SparksAndCode/Lock-Picking-Robot-V2/robot/Lock_Pick_v2 v76 v20_Lock_Pick_v2 v76 v20_5972K173_Ball Bearing_1_Body1.stl

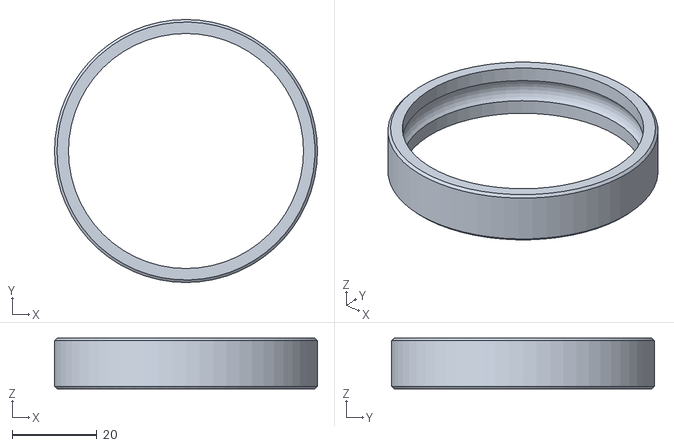
[picture p11: CAD file, 2024-05-01]
robot/Lock_Pick_v2 v76 v20_Lock_Pick_v2 v76 v20_5972K173_Ball Bearing_1_Body1.stl
62.0 x 62.0 x 12.0
