SparksAndCode/Lock-Picking-Robot-V2/robot/Lock_Pick_v2 v76 v20_Lock_Pick_v2 v76 v20_Lock Clamp_1_LockClamp_top.stl

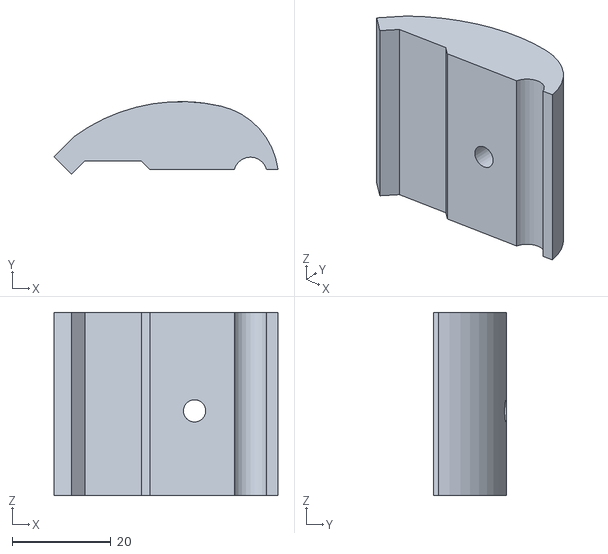
[picture p12: CAD file, 2024-05-01]
robot/Lock_Pick_v2 v76 v20_Lock_Pick_v2 v76 v20_Lock Clamp_1_LockClamp_top.stl
45.3 x 14.7 x 37.0
