SparksAndCode/Lock-Picking-Robot-V2/robot/Lock_Pick_v2 v76 v20_Lock_Pick_v2 v76 v20_Lock Clamp_1_LockClamp_Bottom.stl

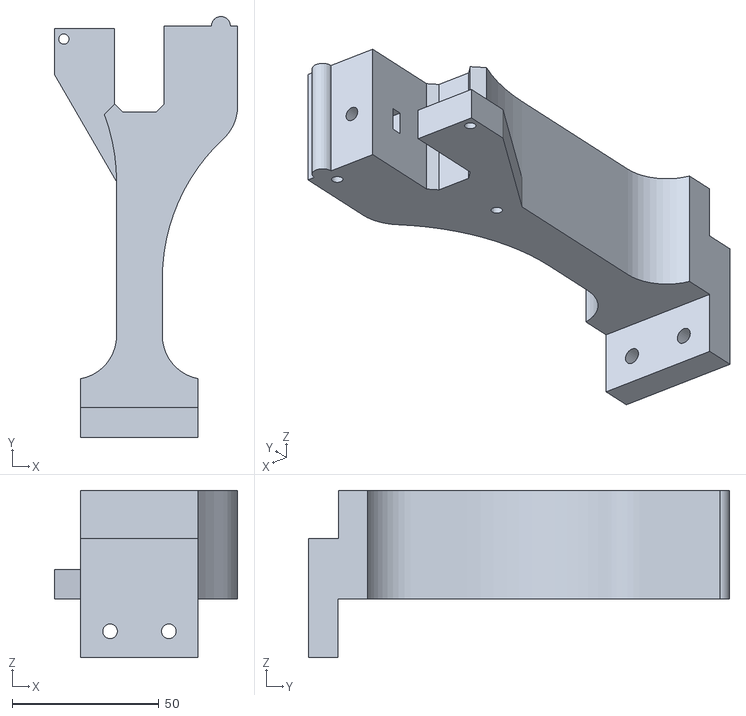
[picture p13: CAD file, 2024-05-01]
robot/Lock_Pick_v2 v76 v20_Lock_Pick_v2 v76 v20_Lock Clamp_1_LockClamp_Bottom.stl
62.4 x 143.3 x 57.0
