SparksAndCode/Lock-Picking-Robot-V2/robot/Lock_Pick_v2 v76 v20_Lock_Pick_v2 v76 v20_Lock_1_Body_1_Body1.stl

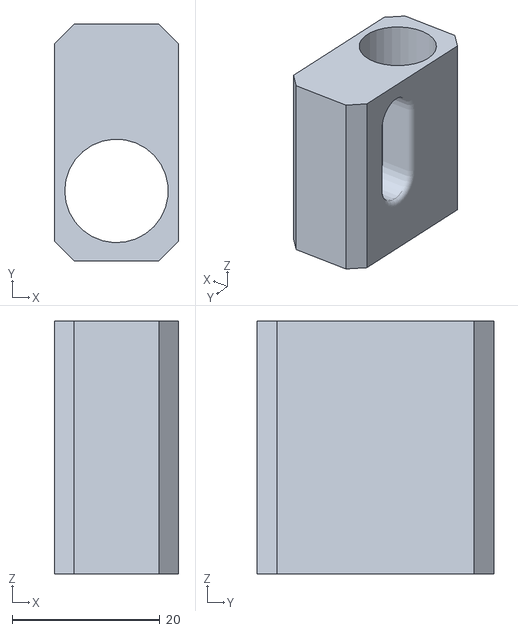
[picture p14: CAD file, 2024-05-01]
robot/Lock_Pick_v2 v76 v20_Lock_Pick_v2 v76 v20_Lock_1_Body_1_Body1.stl
16.8 x 32.0 x 34.2
