SparksAndCode/Lock-Picking-Robot-V2/robot/Lock_Pick_v2 v76 v20_Lock_Pick_v2 v76 v20_5537T032_T-Slotted Framing_1_Body1.stl

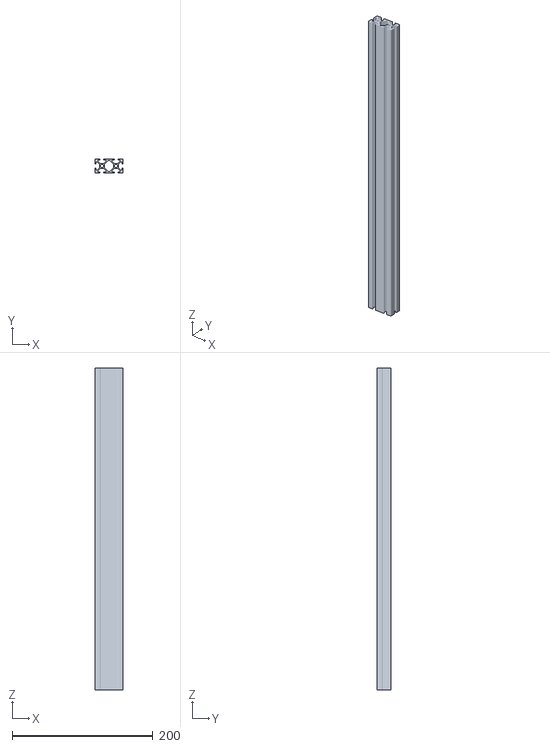
[picture p15: CAD file, 2024-05-01]
robot/Lock_Pick_v2 v76 v20_Lock_Pick_v2 v76 v20_5537T032_T-Slotted Framing_1_Body1.stl
40.0 x 20.0 x 457.2
