SparksAndCode/Lock-Picking-Robot-V2/robot/Lock_Pick_v2 v76 v20_Lock_Pick_v2 v76 v20_BearingBushing_1_bearing_bushing.stl

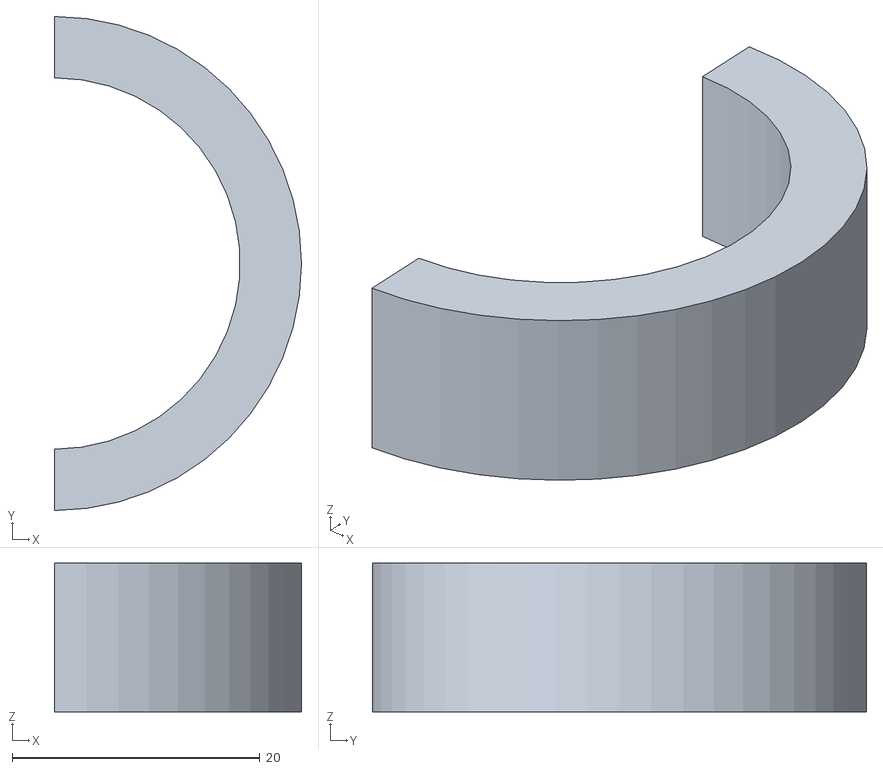
[picture p16: CAD file, 2024-05-01]
robot/Lock_Pick_v2 v76 v20_Lock_Pick_v2 v76 v20_BearingBushing_1_bearing_bushing.stl
20.0 x 39.9 x 12.0
