SparksAndCode/Lock-Picking-Robot-V2/robot/Lock_Pick_v2 v76 v20_Lock_Pick_v2 v76 v20_Nema23_Mount_1_Nema23_mount.stl

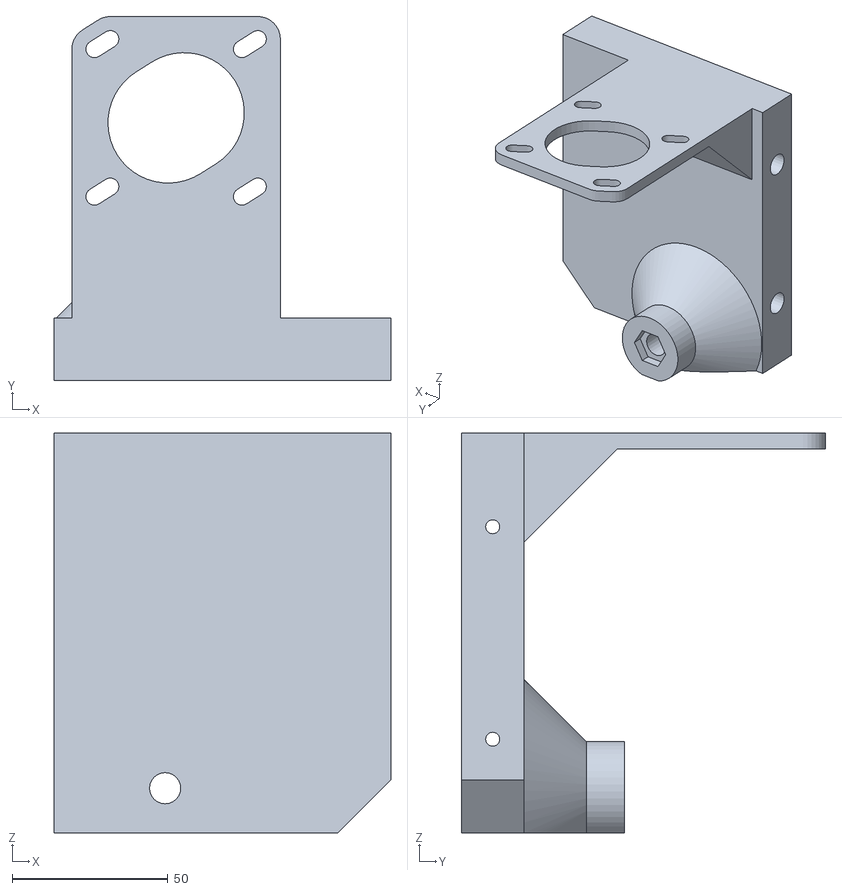
[picture p17: CAD file, 2024-05-01]
robot/Lock_Pick_v2 v76 v20_Lock_Pick_v2 v76 v20_Nema23_Mount_1_Nema23_mount.stl
107.9 x 116.7 x 128.1
