SparksAndCode/Lock-Picking-Robot-V2/robot/Lock_Pick_v2 v76 v20_Lock_Pick_v2 v76 v20_Twist Support_1_Body1.stl

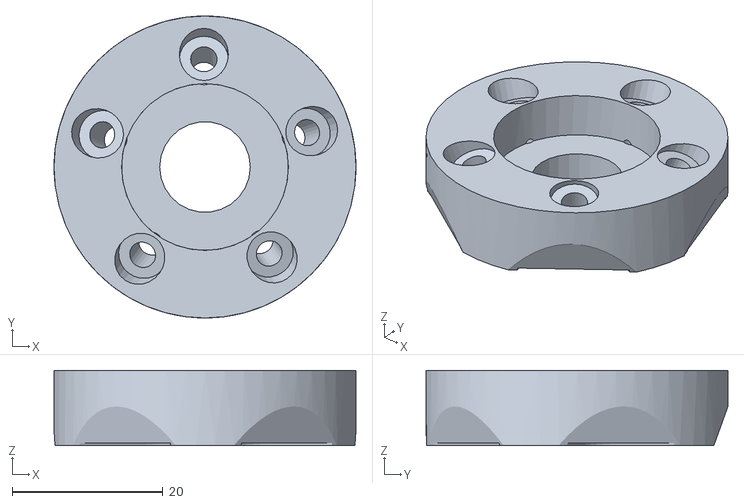
[picture p18: CAD file, 2024-05-01]
robot/Lock_Pick_v2 v76 v20_Lock_Pick_v2 v76 v20_Twist Support_1_Body1.stl
40.0 x 40.0 x 10.0
