SparksAndCode/Lock-Picking-Robot-V2/robot/Lock_Pick_v2 v76 v20_Lock_Pick_v2 v76 v20_Rear Support Lower_1_v-bearing(Mirror)_1_Body1.stl

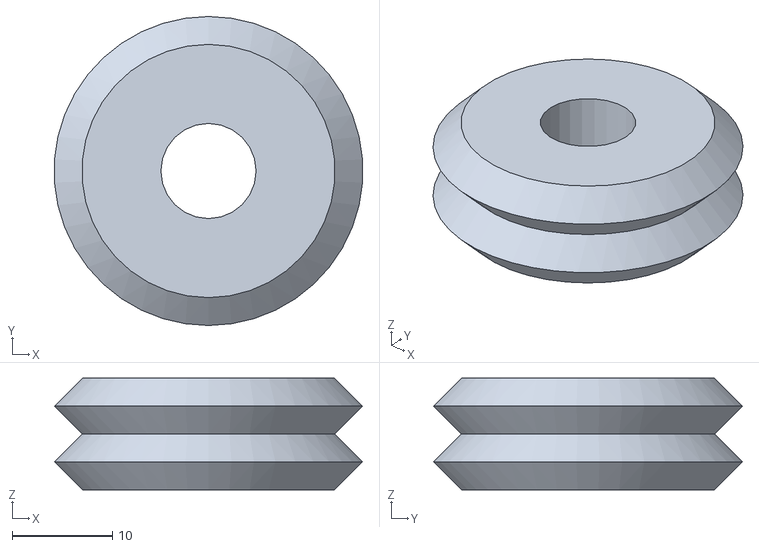
[picture p19: CAD file, 2024-05-01]
robot/Lock_Pick_v2 v76 v20_Lock_Pick_v2 v76 v20_Rear Support Lower_1_v-bearing(Mirror)_1_Body1.stl
30.7 x 30.8 x 11.1
