SparksAndCode/Lock-Picking-Robot-V2/robot/Lock_Pick_v2 v76 v20_Lock_Pick_v2 v76 v20_Healical Gear (35R@22.50)_1_Outer_gear_adapater.stl

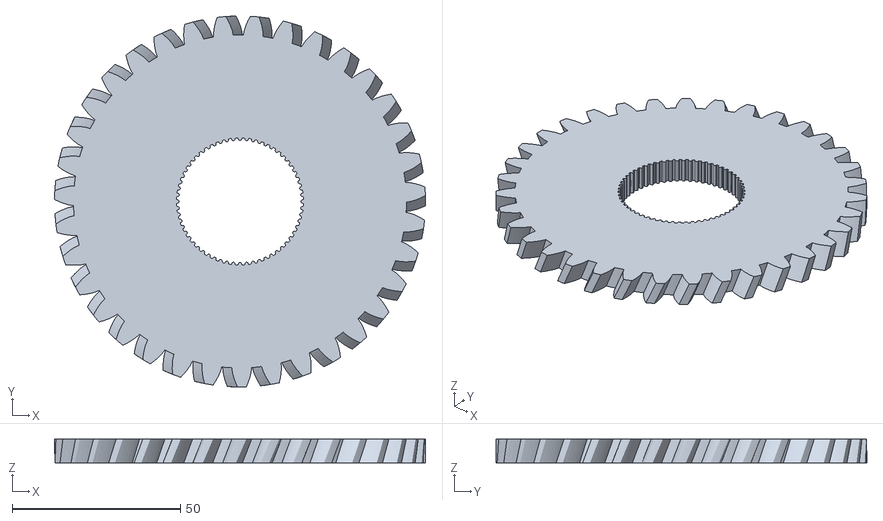
[picture p20: CAD file, 2024-05-01]
robot/Lock_Pick_v2 v76 v20_Lock_Pick_v2 v76 v20_Healical Gear (35R@22.50)_1_Outer_gear_adapater.stl
110.3 x 110.3 x 7.00
