SparksAndCode/Lock-Picking-Robot-V2/robot/Lock_Pick_v2 v76 v20_Lock_Pick_v2 v76 v20_5972K173_Ball Bearing_1_Body15.stl

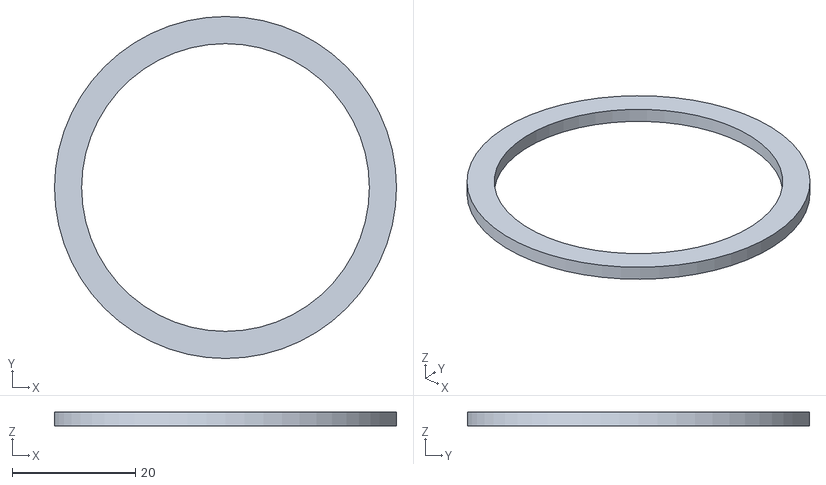
[picture p21: CAD file, 2024-05-01]
robot/Lock_Pick_v2 v76 v20_Lock_Pick_v2 v76 v20_5972K173_Ball Bearing_1_Body15.stl
55.4 x 55.4 x 2.24
