SparksAndCode/Lock-Picking-Robot-V2/robot/Lock_Pick_v2 v76 v20_Lock_Pick_v2 v76 v20_Rear_Bearing_Ring_1_Body2.stl

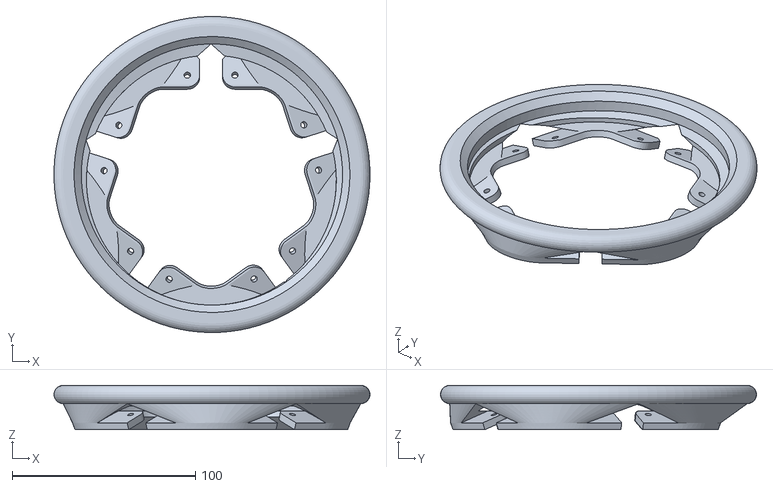
[picture p22: CAD file, 2024-05-01]
robot/Lock_Pick_v2 v76 v20_Lock_Pick_v2 v76 v20_Rear_Bearing_Ring_1_Body2.stl
172.6 x 172.6 x 24.2
