SparksAndCode/Lock-Picking-Robot-V2/robot/Lock_Pick_v2 v76 v20_Lock_Pick_v2 v76 v20_Lock_1_Tumbler_1_Body1.stl

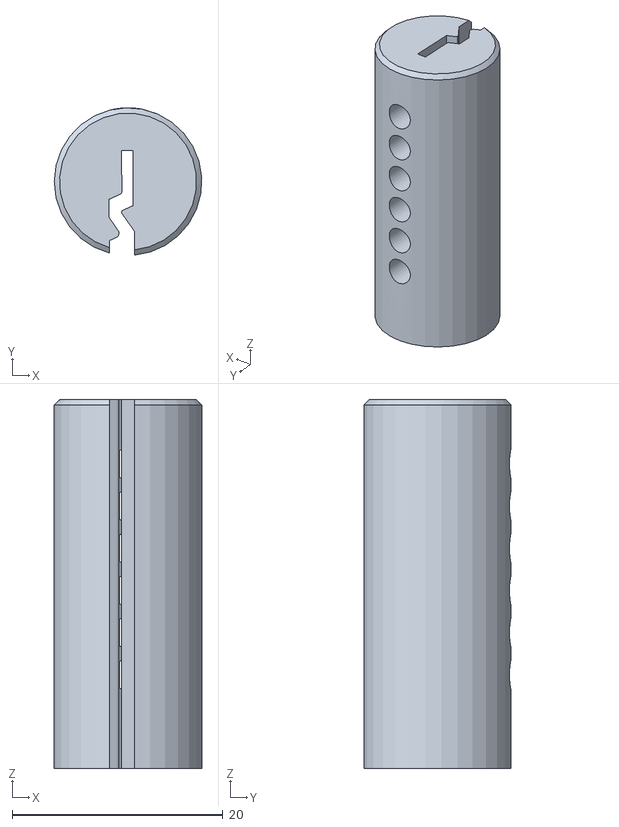
[picture p24: CAD file, 2024-05-01]
robot/Lock_Pick_v2 v76 v20_Lock_Pick_v2 v76 v20_Lock_1_Tumbler_1_Body1.stl
14.0 x 14.0 x 35.0
