SparksAndCode/Lock-Picking-Robot-V2/robot/Lock_Pick_v2 v76 v20_Lock_Pick_v2 v76 v20_Healical Gear (35R@22.50)_1_Body1.stl

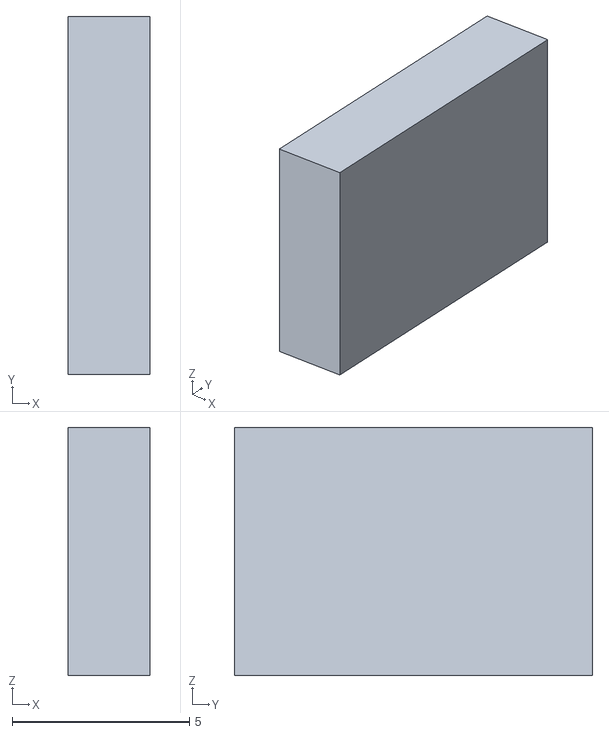
[picture p25: CAD file, 2024-05-01]
robot/Lock_Pick_v2 v76 v20_Lock_Pick_v2 v76 v20_Healical Gear (35R@22.50)_1_Body1.stl
2.30 x 10.1 x 7.00
