SparksAndCode/Lock-Picking-Robot-V2/robot/Lock_Pick_v2 v76 v20_Lock_Pick_v2 v76 v20_BearingSupport_1_front_bearing_support.stl

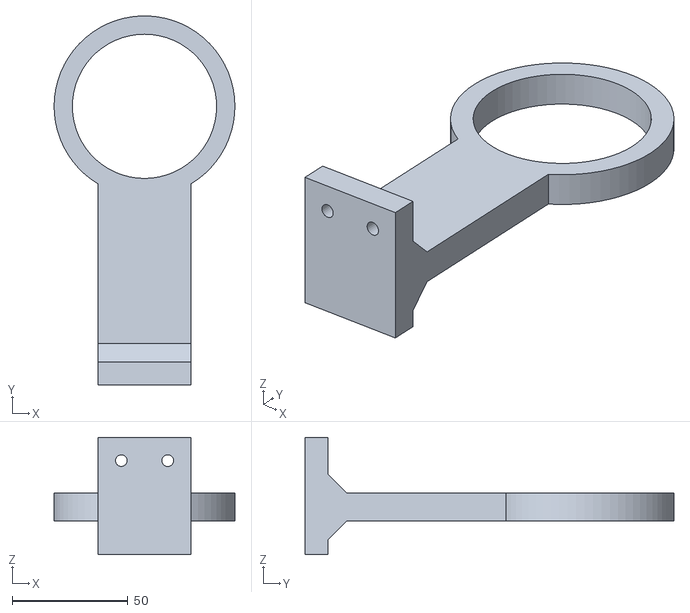
[picture p26: CAD file, 2024-05-01]
robot/Lock_Pick_v2 v76 v20_Lock_Pick_v2 v76 v20_BearingSupport_1_front_bearing_support.stl
78.0 x 159.2 x 50.5
