SparksAndCode/Lock-Picking-Robot-V2/robot/Lock_Pick_v2 v76 v20_Lock_Pick_v2 v76 v20_5972K173_Ball Bearing_1_Body2.stl

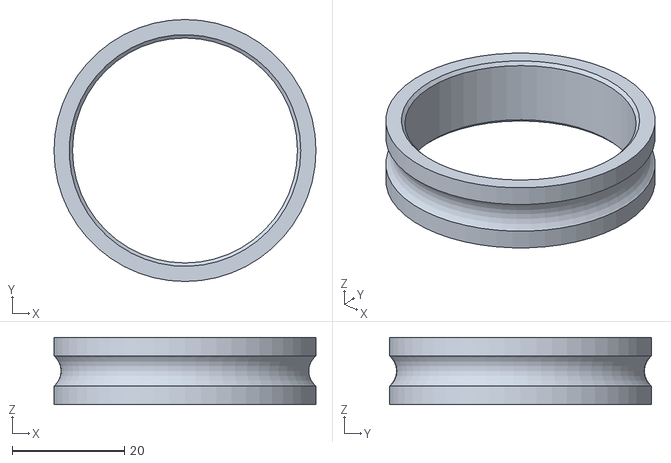
[picture p28: CAD file, 2024-05-01]
robot/Lock_Pick_v2 v76 v20_Lock_Pick_v2 v76 v20_5972K173_Ball Bearing_1_Body2.stl
46.6 x 46.6 x 12.0
