SparksAndCode/Lock-Picking-Robot-V2/robot/Lock_Pick_v2 v76 v20_Lock_Pick_v2 v76 v20_Key_1_KeyBlade.stl

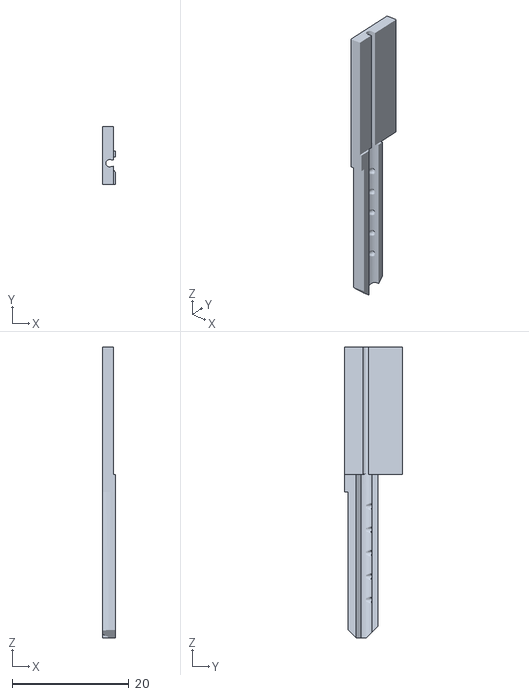
[picture p29: CAD file, 2024-05-01]
robot/Lock_Pick_v2 v76 v20_Lock_Pick_v2 v76 v20_Key_1_KeyBlade.stl
2.30 x 9.92 x 49.8
