SparksAndCode/Lock-Picking-Robot-V2/robot/Lock_Pick_v2 v76 v20_Lock_Pick_v2 v76 v20_Lock Clamp_1_EncoderStraightAdapter_1_EncoderStraightAdapater.stl

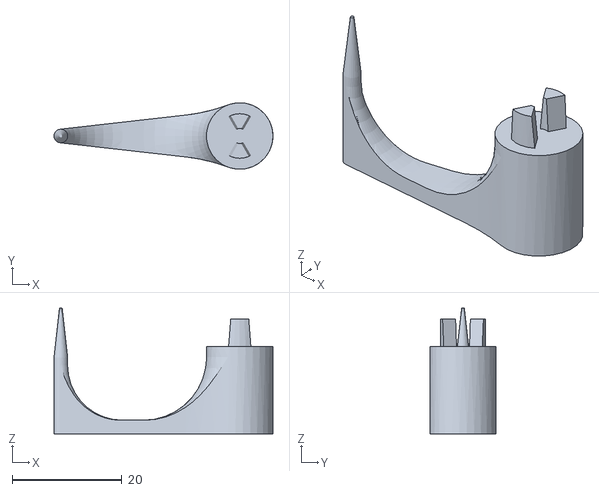
[picture p30: CAD file, 2024-05-01]
robot/Lock_Pick_v2 v76 v20_Lock_Pick_v2 v76 v20_Lock Clamp_1_EncoderStraightAdapter_1_EncoderStraightAdapater.stl
40.0 x 12.1 x 23.0
