SparksAndCode/Lock-Picking-Robot-V2/robot/Lock_Pick_v2 v76 v20_Lock_Pick_v2 v76 v20_Lock Clamp_1_Encoder (1)_1_Body1.stl

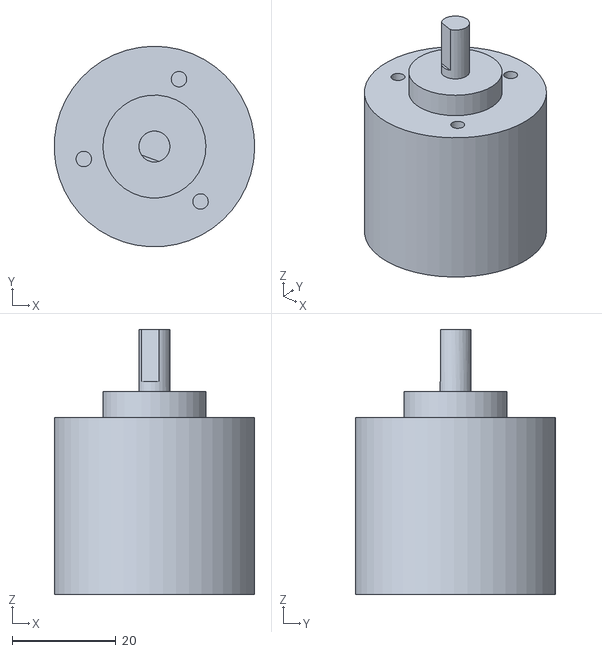
[picture p31: CAD file, 2024-05-01]
robot/Lock_Pick_v2 v76 v20_Lock_Pick_v2 v76 v20_Lock Clamp_1_Encoder (1)_1_Body1.stl
38.7 x 38.7 x 51.2
