SparksAndCode/Lock-Picking-Robot-V2/robot/Lock_Pick_v2 v76 v20_Lock_Pick_v2 v76 v20_Rear Support Lower_1_Mount_1_Body1.stl

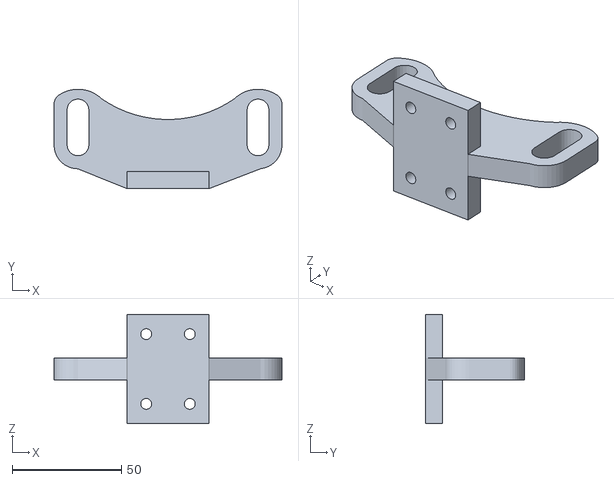
[picture p32: CAD file, 2024-05-01]
robot/Lock_Pick_v2 v76 v20_Lock_Pick_v2 v76 v20_Rear Support Lower_1_Mount_1_Body1.stl
104.5 x 45.6 x 50.0
