SparksAndCode/Lock-Picking-Robot-V2/robot/Lock_Pick_v2 v76 v20_Lock_Pick_v2 v76 v20_Lock Clamp_1_Encoder Adapter_1_EncoderHolder.stl

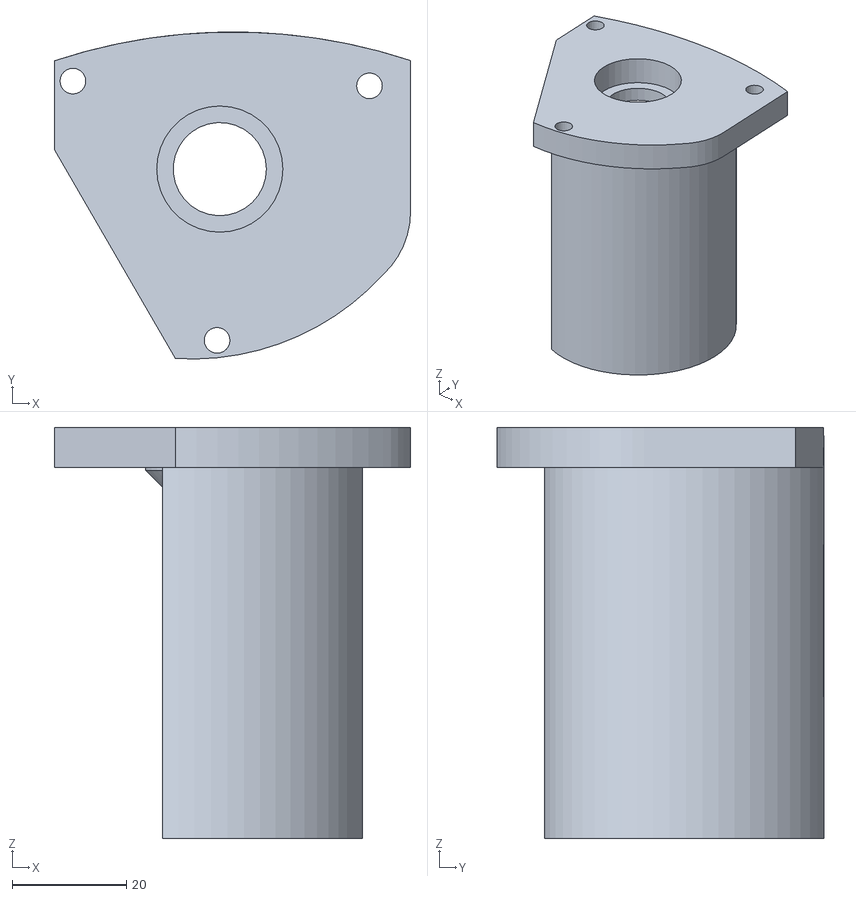
[picture p33: CAD file, 2024-05-01]
robot/Lock_Pick_v2 v76 v20_Lock_Pick_v2 v76 v20_Lock Clamp_1_Encoder Adapter_1_EncoderHolder.stl
62.4 x 57.3 x 72.0
